erikpt/open-adsb-wall/enclosure/preview/blender_back.png

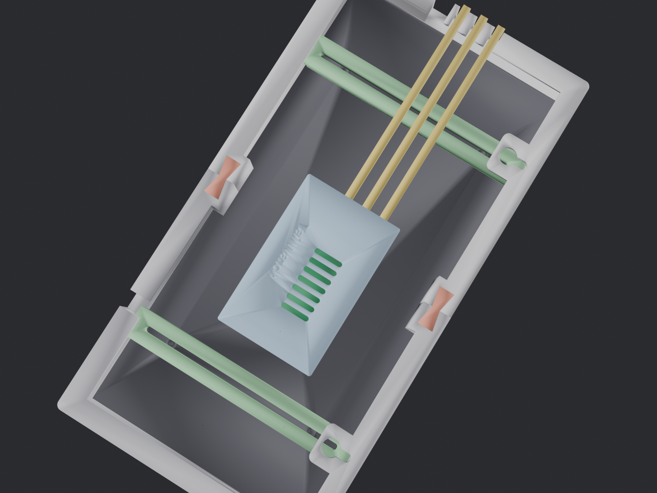
enclosure/preview/blender_back.png
