erikpt/open-adsb-wall/enclosure/preview/frame_left.png

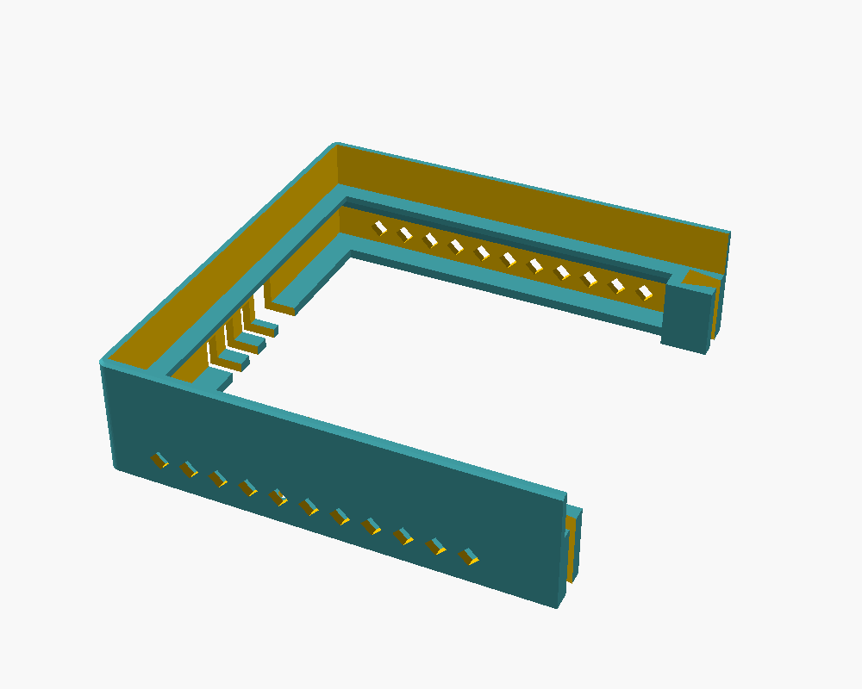
enclosure/preview/frame_left.png
