erikpt/open-adsb-wall/enclosure/preview/strap.png

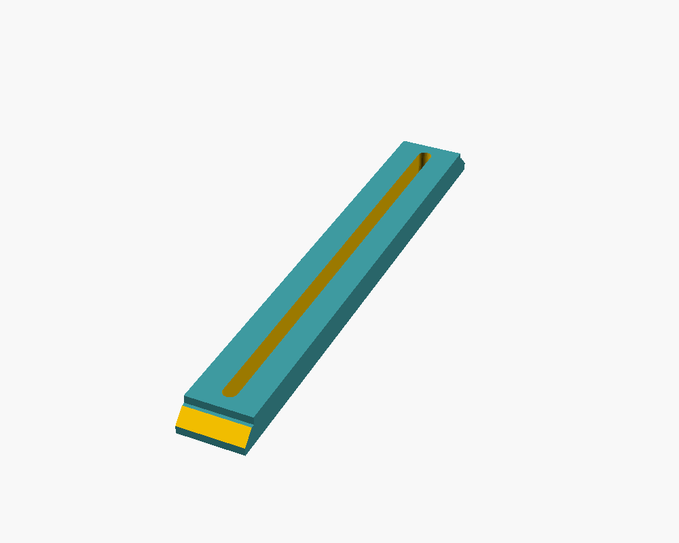
enclosure/preview/strap.png
