erikpt/open-adsb-wall/enclosure/blender_import/button_rods.stl

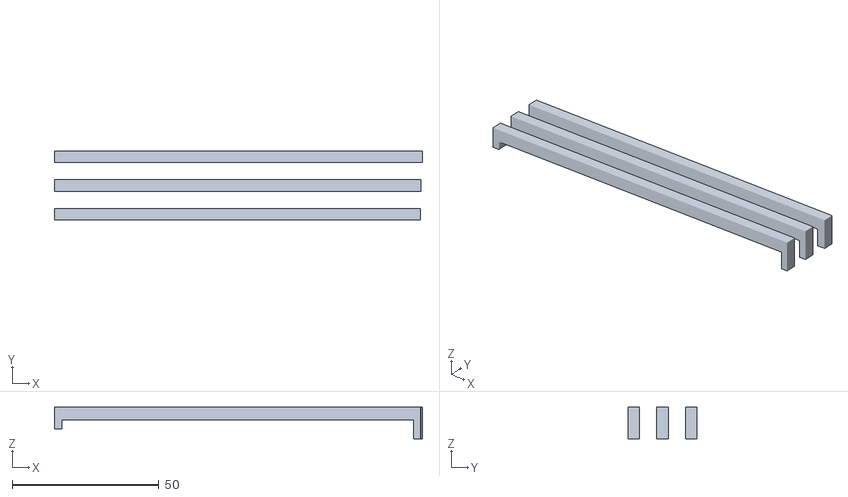
[picture p25: CAD file, 2026-09-26]
enclosure/blender_import/button_rods.stl
125.5 x 23.6 x 10.9
