erikpt/open-adsb-wall/enclosure/button_rods.scad

// TailWatch S3 enclosure -- button_rods
// Button push-rods (DN, UP, RST). Lying flat as exported.
// Exported in print orientation; no supports needed.
include <tailwatch_lib.scad>
run_checks();
rods_print();
