erikpt/open-adsb-wall/enclosure/frame_left.scad

// TailWatch S3 enclosure -- frame_left
// Left frame half (seen from the back: the half with x < seam_x). Rear face down.
// Exported in print orientation; no supports needed.
include <tailwatch_lib.scad>
run_checks();
frame_print(0);
