erikpt/open-adsb-wall/enclosure/portal_pod.scad

// TailWatch S3 enclosure -- portal_pod
// MatrixPortal S3 pod / button-rod guide. Roof down.
// Exported in print orientation; no supports needed.
include <tailwatch_lib.scad>
run_checks();
pod_print();
