erikpt/open-adsb-wall/enclosure/strap.scad

// TailWatch S3 enclosure -- strap
// Rear strap. Print one per entry in strap_xs (default 2). Flat face down.
// Exported in print orientation; no supports needed.
include <tailwatch_lib.scad>
run_checks();
strap_print();
