erikpt/open-adsb-wall/enclosure/blender_import/bowtie_key_2_positioned.scad

// TailWatch S3 enclosure -- bowtie key #2 (top seam boss, s=1), ASSEMBLY position.
include <../tailwatch_lib.scad>
translate([seam_x, panel_h + C - boss_d/2 + 0.5, zf + 0.25]) bowtie_key();
