erikpt/open-adsb-wall/enclosure/blender_import/frame_left_positioned.scad

// TailWatch S3 enclosure -- frame_left, ASSEMBLY position (not print orientation).
// Generated for Blender import; matches assembly() in tailwatch_lib.scad (explode=0).
include <../tailwatch_lib.scad>
frame_half(0);
