erikpt/open-adsb-wall/enclosure/blender_import/frame_right_positioned.scad

// TailWatch S3 enclosure -- frame_right, ASSEMBLY position.
include <../tailwatch_lib.scad>
frame_half(1);
