erikpt/open-adsb-wall/enclosure/blender_import/panel_dummy_positioned.scad

// TailWatch S3 enclosure -- reference panel dummy (not printed), ASSEMBLY position.
include <../tailwatch_lib.scad>
panel_dummy();
