erikpt/open-adsb-wall/enclosure/blender_import/portal_dummy_positioned.scad

// TailWatch S3 enclosure -- reference MatrixPortal dummy (not printed), ASSEMBLY position.
include <../tailwatch_lib.scad>
portal_dummy();
