erikpt/open-adsb-wall/enclosure/blender_import/portal_pod_positioned.scad

// TailWatch S3 enclosure -- portal_pod, ASSEMBLY position.
include <../tailwatch_lib.scad>
on_board() pod_raw();
