erikpt/open-adsb-wall/enclosure/blender_import/strap_1_positioned.scad

// TailWatch S3 enclosure -- strap #1 (strap_xs[0]), ASSEMBLY position.
include <../tailwatch_lib.scad>
translate([strap_xs[0], 0, 0]) strap_raw();
