erikpt/open-adsb-wall/enclosure/blender_import/strap_2_positioned.scad

// TailWatch S3 enclosure -- strap #2 (strap_xs[1]), ASSEMBLY position.
include <../tailwatch_lib.scad>
translate([strap_xs[1], 0, 0]) strap_raw();
