erikpt/open-adsb-wall/firmware/boot.py

# boot.py -- runs once on hard reset / power-up (not on soft reload).
# Default: remount CIRCUITPY read-write for code.py so /prefs.json and
# /prefs.bak can be saved. The USB host then sees the drive as read-only.
# Hold the UP button while pressing RESET (or while powering up) to skip
# the remount: the USB drive stays writable for updating code/lib/www,
# and prefs saves from the web UI will fail until the next normal boot.
import board
import digitalio
import storage

usb_write = False
try:
    btn = digitalio.DigitalInOut(board.BUTTON_UP)
    btn.switch_to_input(pull=digitalio.Pull.UP)
    usb_write = not btn.value  # active-low: pressed == False
    btn.deinit()
except Exception as e:  # missing pin name etc. -> fail safe (USB writable)
    print("boot: button read failed", e)
    usb_write = True

if usb_write:
    print("boot: UP held -> CIRCUITPY writable over USB, read-only to code.py")
else:
    storage.remount("/", readonly=False)
    print("boot: CIRCUITPY writable by code.py, read-only over USB")
